HBprojects/Vectorial-Plot-Rpi-Pico/kicad/vecpico.kicad_sch

## KiCad design kicad/vecpico.kicad_sch (2026-01-16)

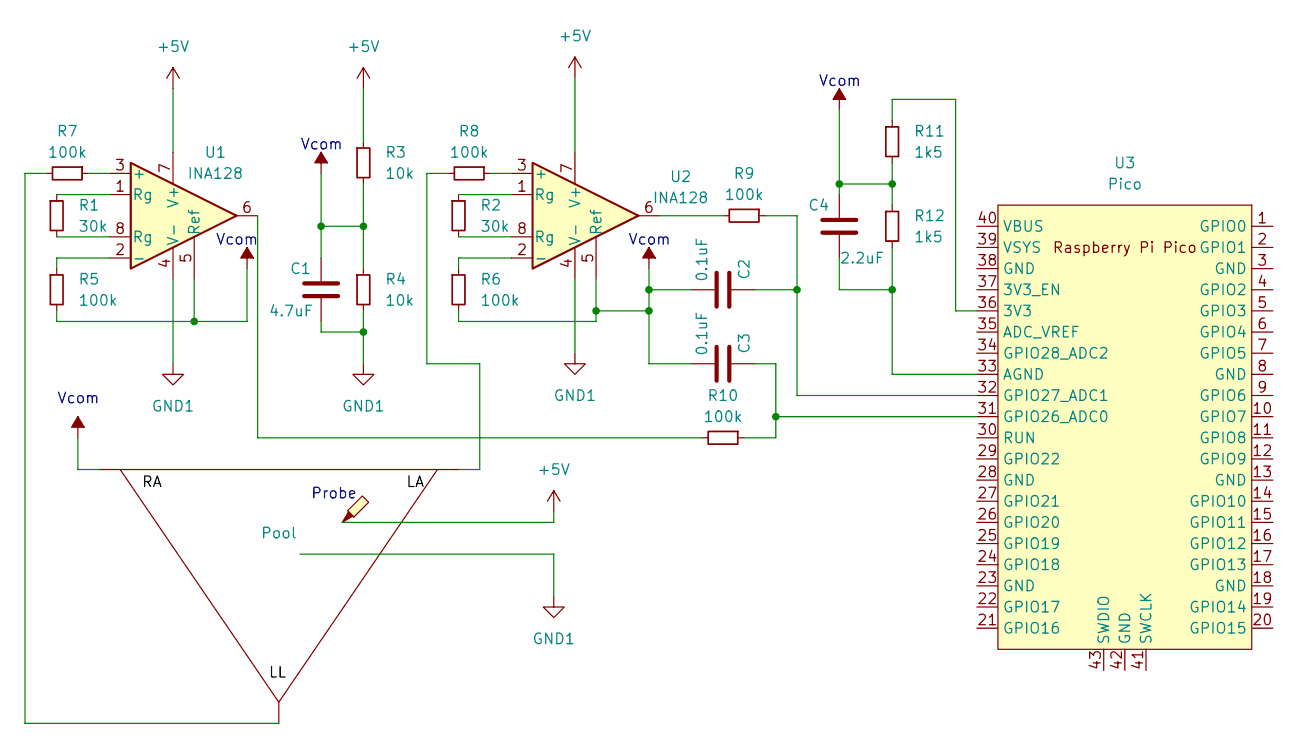
[picture p5: schematic vecpico.kicad_sch]

Parts:
C1: 4.7uF
C2, C3: 0.1uF
C4: 2.2uF
R1, R2: 30k
R3, R4: 10k
R5, R6, R7, R8, R9, R10: 100k
R11, R12: 1k5
U1, U2: INA128
U3: Pico; RPi_Pico_SMD_TH

Connections:
unnamed: C1.1, R3.2, R4.1
unnamed: C1.2, R4.2
unnamed: C2.1, R9.1, U3.32 (GPIO27_ADC1)
unnamed: C2.2, C3.2, R6.2, U2.5 (Ref)
unnamed: C3.1, R10.1, U3.31 (GPIO26_ADC0)
unnamed: C4.1, R11.2, R12.1
unnamed: C4.2, R12.2, U3.33 (AGND)
unnamed: R1.1, U1.1 (Rg)
unnamed: R1.2, U1.8 (Rg)
unnamed: R2.1, U2.1 (Rg)
unnamed: R2.2, U2.8 (Rg)
unnamed: R5.1, U1.2 (-)
unnamed: R5.2, U1.5 (Ref)
unnamed: R6.1, U2.2 (-)
unnamed: R7.1, U1.3 (+)
unnamed: R8.1, U2.3 (+)
unnamed: R9.2, U2.6
unnamed: R10.2, U1.6
unnamed: R11.1, U3.36 (3V3)

Notes on the sheet:
Vcom
Probe
