HBprojects/Vectorial-Plot-Rpi-Pico/firmware/demo_signal_pico.py

import utime

# Segment 1: The ECG Signal Data
# We use a tuple of tuples for better memory efficiency on the Pico
# Fixed Segment 1: All inner braces replaced with parentheses
ECG_SIGNAL1 = (
    (53,79),(52,78),(50,76),(47,74),(44,72),(41,70),(37,68),(34,67),(31,66),(28,65),(26,64),(24,62),(22,60),(21,58),(20,55),(19,52),(19,49),(18,45),(17,42),(16,39),(15,36),(14,35),(13,34),(12,35),(11,37),(10,40),(9,43),(9,46),(9,50),(9,52),(10,54),(11,54),(4,53),(4,51),(5,48),(5,44),(5,39),(5,35),(5,31),(5,27),(5,24),(5,22),(5,21),(5,20),(5,20),(4,21),(4,22),(4,24),(3,27),(3,29),(3,32),(2,35),(2,39),
    (2,42),(2,45),(2,47),(2,49),(4,51),(4,52),(5,52),(5,53),(5,53),(5,52),(5,52),(5,52),(5,52),(5,52),(5,52),(5,52),(5,51),(5,50),(5,48),(4,45),(20,41),(26,36),(44,29),(68,22),(98,14),(133,8),(174,2),(224,0),(283,116),(355,160),(440,246),(540,378),(653,556),(778,777),(912,1036),(1013,1328),(1160,1644),(1258,1975),(1572,2313),(1789,2647),(2068,2968),(2348,3268),(2627,3539),(2858,3775),(3040,3974),
    (3221,4133),(3333,4254),(3445,4341),(3557,4399),(3669,4434),(3725,4453),(3781,4463),(3822,4469),(3850,4476),(3864,4484),(3878,4493),(3892,4500),(3906,4500),(3836,4487),(3822,4452),(3809,4389),(3795,4290),(3767,4151),(3739,3968),(3683,3741),(3627,3471),(3515,3162),(3403,2819),(3291,2449),(3169,2059),(3006,1658),(2797,1283),(2539,902),(2233,545),(1934,218),(1530,-70),(1152,-312),(815,-505),
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
)

SCALE_FACTOR = 0.000435
TARGET_POINTS = 680

def interpolate_signal(original_data, target_size):
    """
    Increases the resolution of the signal using linear interpolation.
    """
    n = len(original_data)
    interpolated = []
    
    for i in range(target_size):
        # Calculate the relative position in the original array
        # 490 / 735 = 0.666...
        float_index = i * (n - 1) / (target_size - 1)
        index = int(float_index)
        fraction = float_index - index
        
        if index >= n - 1:
            interpolated.append(original_data[n-1])
        else:
            # Interpolate both Wave 0 and Wave 1
            p1 = original_data[index]
            p2 = original_data[index + 1]
            
            # Formula: p1 + (p2 - p1) * fraction
            w0 = p1[0] + (p2[0] - p1[0]) * fraction
            w1 = p1[1] + (p2[1] - p1[1]) * fraction
            interpolated.append((w0, w1))
            
    return interpolated

def run_signal_transmission():
    # Generate the 735 points version
    print("Resampling signal to 735 points...")
    signal_735 = interpolate_signal(ECG_SIGNAL1, TARGET_POINTS)
    print("Starting transmission...")

    while True:
        for row in signal_735:
            # Row[0] and Row[1] are now floats from interpolation
            wave0 = row[0] * SCALE_FACTOR
            wave1_raw = row[1] * SCALE_FACTOR
            
            wave2 = wave1_raw - wave0
            wave1 = wave1_raw * -1

            # Output 5 decimal values
            print("{:.5f}, {:.5f}, {:.5f}".format(wave0, wave1, wave2))

            # Adjusted delay: 
            # If you want the wave to last the same total time as before:
            # (490 pts * 32ms) / 735 pts = ~21ms
            utime.sleep_ms(5)

if __name__ == "__main__":
    run_signal_transmission()
